NoahVastmans/Health-Tech/Video Tracking/Output gifs/IMG_5481_1046AM_Cut_tracked.gif

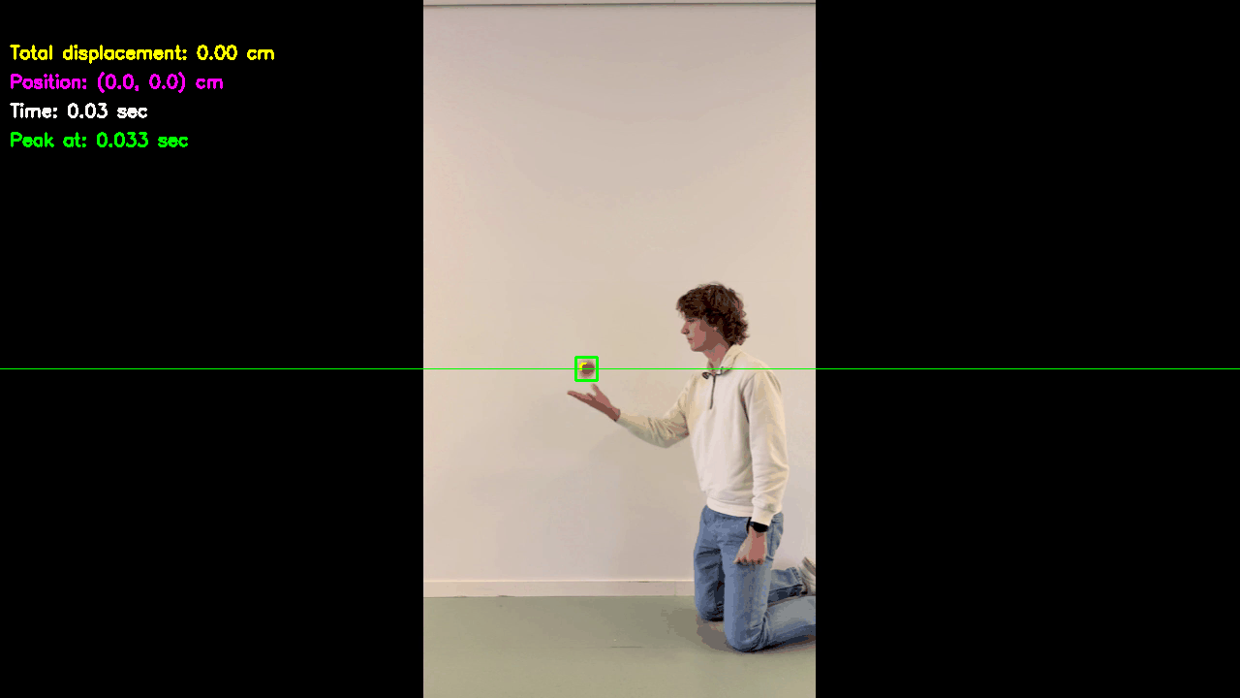
Video Tracking/Output gifs/IMG_5481_1046AM_Cut_tracked.gif
